brandysnaps/ratchet-and-clank-lightbox/docs/assets/images/a-team.jpg

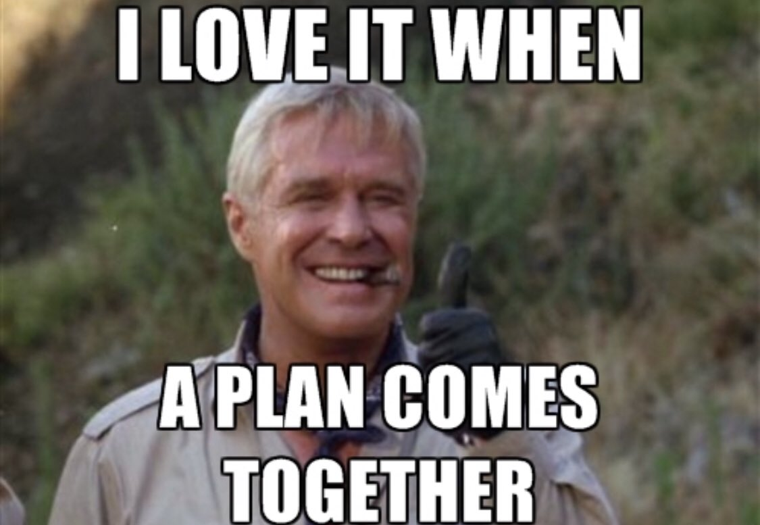
docs/assets/images/a-team.jpg
