brandysnaps/ratchet-and-clank-lightbox/docs/assets/images/circuit-python.png

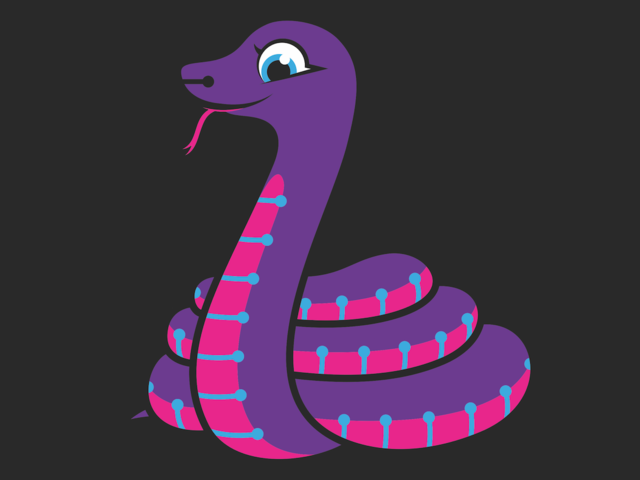
docs/assets/images/circuit-python.png
