brandysnaps/ratchet-and-clank-lightbox/docs/assets/images/cover-img-1.jpg

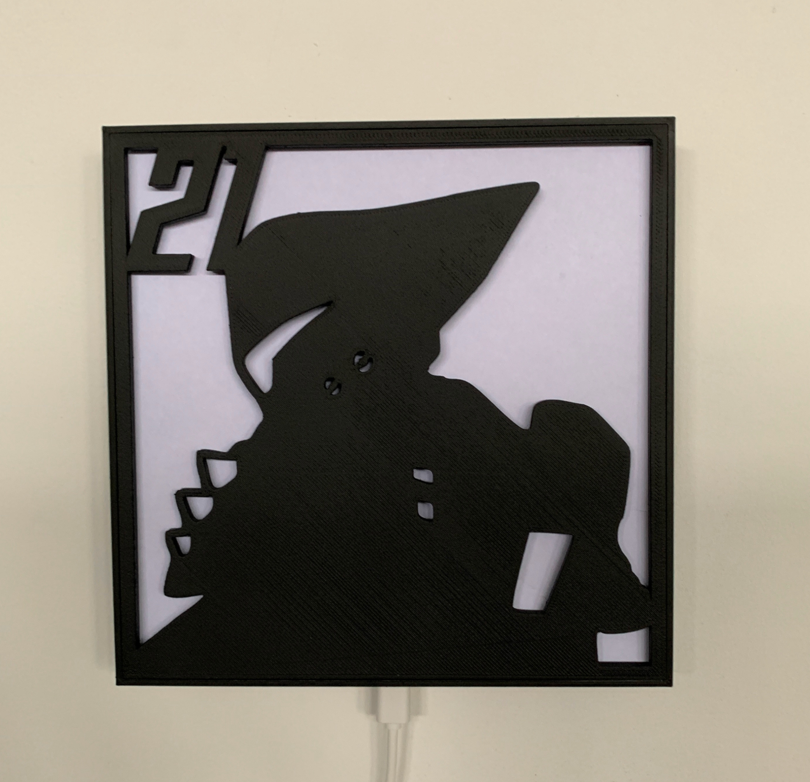
docs/assets/images/cover-img-1.jpg
