brandysnaps/ratchet-and-clank-lightbox/docs/assets/images/cover-img-2.jpg

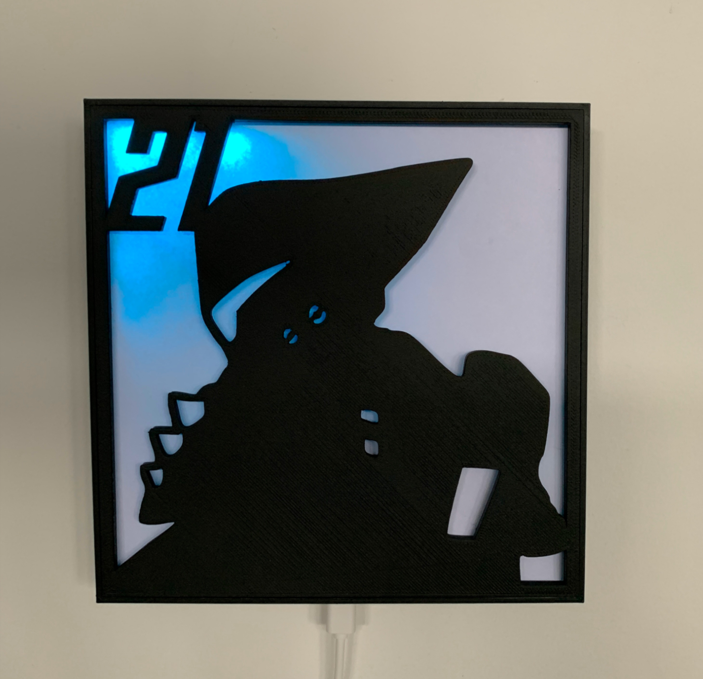
docs/assets/images/cover-img-2.jpg
