brandysnaps/ratchet-and-clank-lightbox/docs/assets/images/cover-img-3.jpg

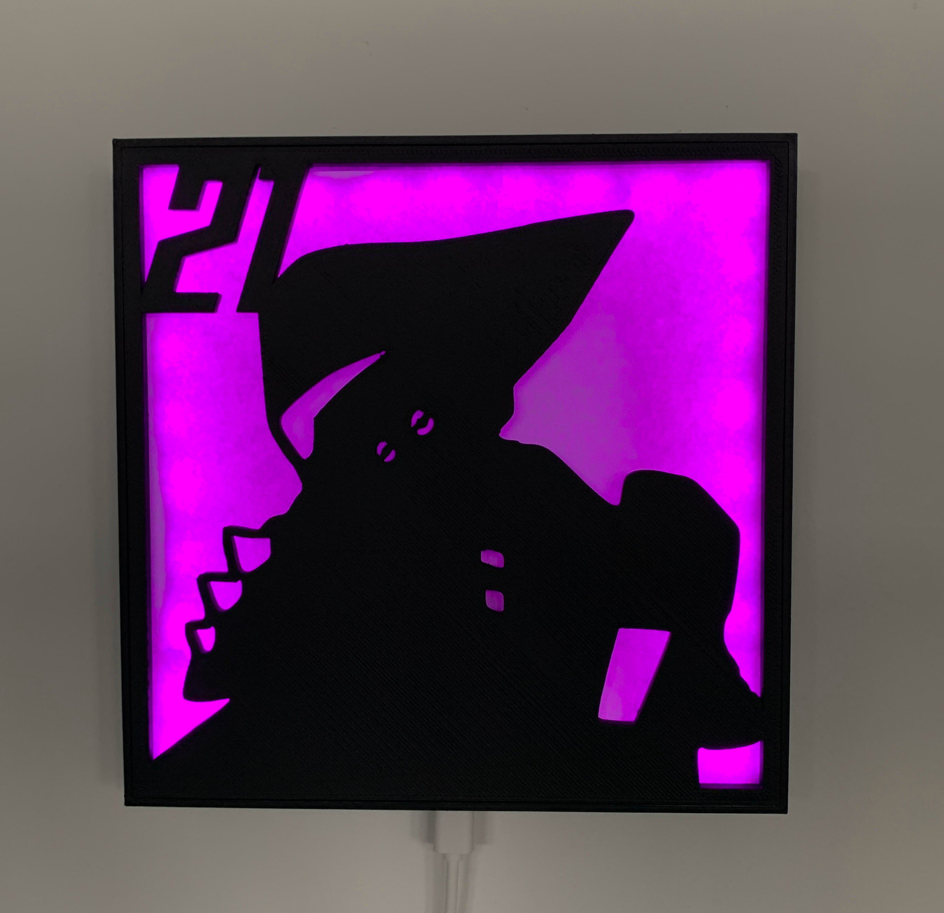
docs/assets/images/cover-img-3.jpg
