brandysnaps/ratchet-and-clank-lightbox/docs/assets/images/cover-img-4.jpg

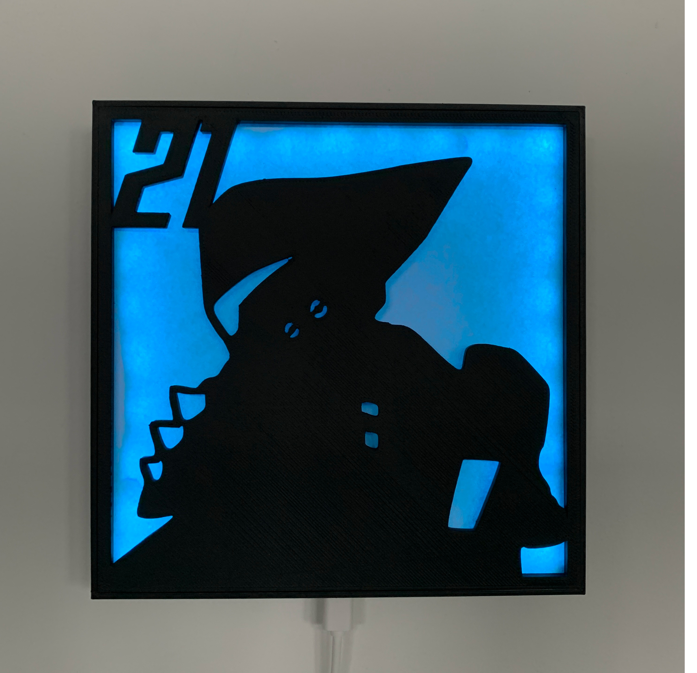
docs/assets/images/cover-img-4.jpg
