brandysnaps/ratchet-and-clank-lightbox/docs/assets/images/introduction.jpg

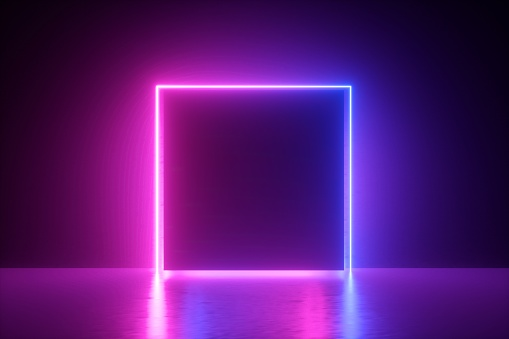
docs/assets/images/introduction.jpg
