brandysnaps/ratchet-and-clank-lightbox/docs/assets/images/lightbox-inspiration.jpg

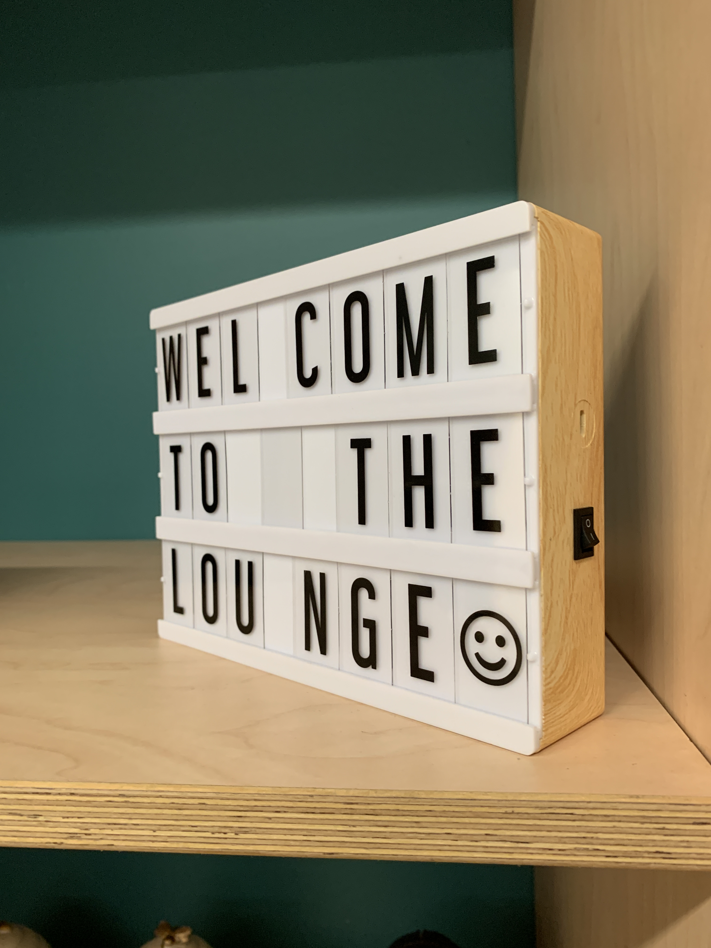
docs/assets/images/lightbox-inspiration.jpg
