brandysnaps/ratchet-and-clank-lightbox/docs/assets/images/maths.gif

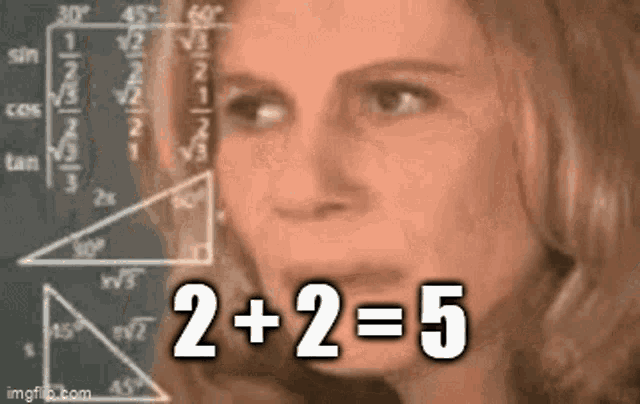
docs/assets/images/maths.gif
