brandysnaps/ratchet-and-clank-lightbox/docs/assets/images/micropython-pico-thumbnail.jpg

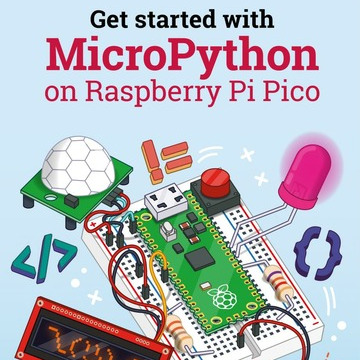
docs/assets/images/micropython-pico-thumbnail.jpg
