brandysnaps/ratchet-and-clank-lightbox/docs/assets/images/octoprint.png

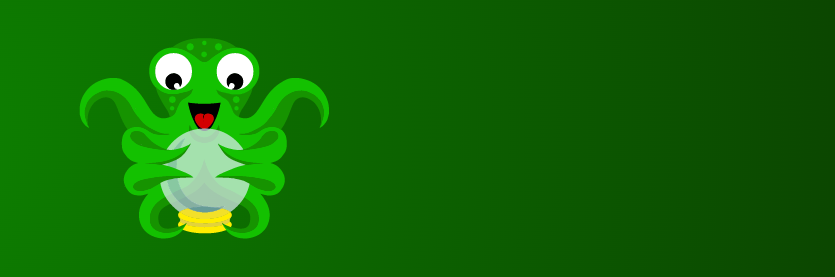
docs/assets/images/octoprint.png
