brandysnaps/ratchet-and-clank-lightbox/docs/assets/images/spiderman-spray-paint.jpg

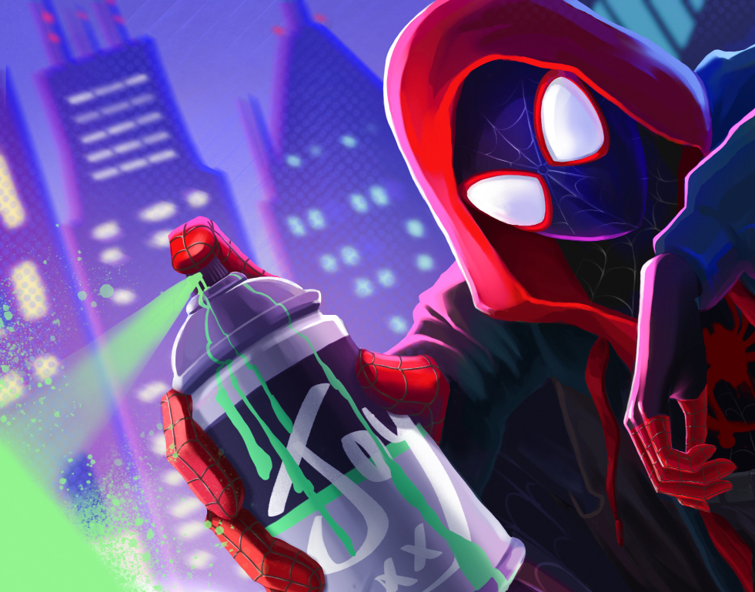
docs/assets/images/spiderman-spray-paint.jpg
