brandysnaps/ratchet-and-clank-lightbox/docs/assets/images/website_thumbnail.png

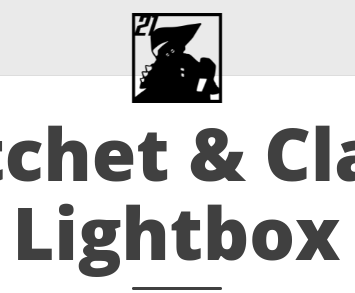
docs/assets/images/website_thumbnail.png
