brandysnaps/ratchet-and-clank-lightbox/docs/assets/images/boxed-2.jpg

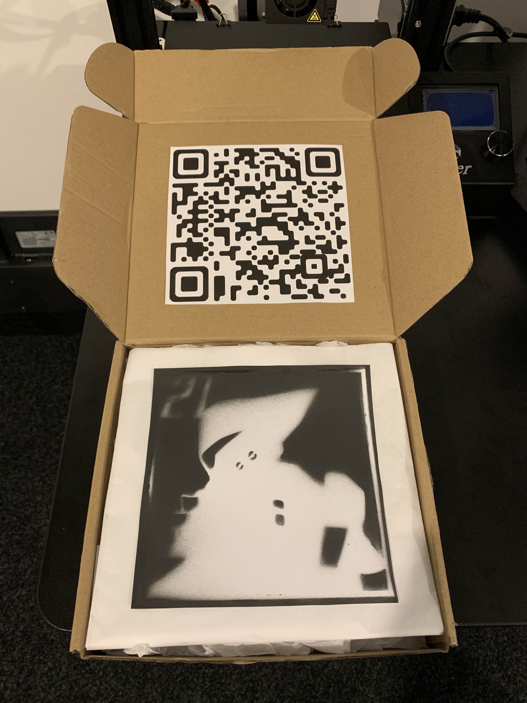
[picture p53: docs/assets/images/boxed-2.jpg]
docs/assets/images/boxed-2.jpg
